daniw/scrutester/hw/ST1-1/Admin/STM32G474 pinout.xlsx

Sheet: Functions
Function | Pin type | Pin quantity | Necessary | Assigned | Remarks
BMS
BMS communication | I2C | 2 | 1 |  | Also connects to EEPROM
BMS wakeup | GPIO | 1 | 1
I_BAT | ADC | 1 | 1
On / off controller
On request | GPIO | 1 | 1
V_IN | ADC | 1 | 1
Converter
Buck-Boost PWM | HRTIM | 4 | 1 | 1 | One channel per bridge
Converter Temperature | ADC | 3 | 1 |  | Number of channels might change
Enable | GPIO | 1 | ? |  | Converter enable still necessary?
Discharge | GPIO | 1 | 1
High voltage converter
Flyback PWM | HRTIM | 1 | 1 | 1
Enable | GPIO | 1 | ? |  | Flyback enable still necessary?
V_HV | ADC | 1 | 1
Overvoltage protection
OVP latch | GPIO | 1 | 1
OVP reset | GPIO | 1 | 1
Current controller
I_1A_REF | DAC | 1 | 1
Shunt enable | GPIO | 1 | 1
Shunt iso enable | GPIO | 1 | 1
Controller temperature | ADC | 1 | 1
Output terminal
V_OUT | ADC | 1 | 1 |  | This measurement does not cover the full output voltage range
OUT_SEL_HV | GPIO | 1 | 1
OUT_SEL_ISO | GPIO | 1 | 1
Measurement
ADC interface | SPI | 4 | 1 | 1
ADC control | GPIO | 3 | 1
V_TERM | ADC | 1 | 1
I_OUT | ADC | 1 | 1
I_ISO | ADC | 1 | 1
User interface
Display | SPI | 4 | 1 | 1
Interface | I2C | 0 | 1 | 0 | Interface shared with BMS
Serial interface | USART | 2 | 1
Encoder | TIM | 2 | 1 | 0.5 | TIM3 or 4
Button | GPIO | 3 | 1
UI present | GPIO | 1 | 1
Infrared interface | IrDA | 2 | 0 |  | USART1, 2, 3, 4, or 5
Microcontroller
Flash | QSPI | 6 | 1 | 1
Programming interface | SWD / JTAG | 4 | 1 | 1
EEPROM | I2C | 0 | 1 | 0 | Interface shared with BMS
Reset | Reset | 1 | 1

Sheet: Timer
Timer overview
Timer Type | Timer | Length | Counter type | Prescaler | Capture / compare channels | Complementary outputs | Encoder
High resolution timer | HRTIM | 16 | Up | 1, 2, 4, (x2, x4, x8, x16, x32 with DLL) | 12 | Yes | No
Advanced motor control | TIM1, TIM8, TIM20 | 16 | Up, down, Up/down | Integer between 1 and 65536 | 4 | 4 | No
General-purpose | TIM2, TIM5 | 32 | Up, down, Up/down | Integer between 1 and 65536 | 4 | No | Yes
General-purpose | TIM3, TIM4 | 16 | Up, down, Up/down | Integer between 1 and 65536 | 4 | No | Yes
General-purpose | TIM15 | 16 | Up | Integer between 1 and 65536 | 2 | 1 | No
General-purpose | TIM16, TIM17 | 16 | Up | Integer between 1 and 65536 | 1 | 2 | No
Basic | TIM6, TIM7 | 16 | Up | Integer between 1 and 65536 | 0 | No | No

Sheet: UART
UART Module | Available RX | Available TX
USART1 | PC5, PE1, (PB7) | PC4, PE0, (PB6)
USART2 | PD6, (PB4) | PD5
UART3 | PB8 | PB9
UART4 | Blocked by SPI | Blocked by SPI
UART5 | PD2 | Blocked by SPI

Sheet: ADC index B
ADC
 |  |  | Signal usage
Signal | Description | Speed | Voltage mode | Current mode | Isolation test | 4W resistance | Voltmeter | Ampmeter | Charging | ADC
V_IN | Input voltage | Fast | Feedforward | Feedforward |  | Feedforward |  |  | Control | 3
V_HV | High-voltage DC-link voltage | Fast |  |  | Control |  |  |  |  | 4
V_TERM | Voltage on output terminals (unfused) | Fast | Control | Control | Control | Feedforward | Validate? |  | Feedforward | 2
I_OUT | Output current (high range) | Fast | Control | Control |  | Control |  | Validate? |  | 1
I_ISO | Isolation measurement current | Fast |  |  | Control |  |  |  |  | 5 | Change to | 3
V_OUT | Output voltage (before fuse) | Fast | Protection |  |  | Control |  |  |  | 4
BMS.I_BAT | Battery current | Fast |  |  |  |  |  |  | Control | 5 | Change to | 2
TEMP_CURRENT | Current controller temperature | Slow |  |  |  | Protection |  |  |  | 3, 4, 5
CONV_CTRL.TEMP_PRIM | Primary MOSFET temperature | Slow | Protection | Protection | Protection | Protection |  |  | Protection | 3, 4, 5
CONV_CTRL.TEMP_SEC | Secondary MOSFET temperature | Slow | Protection | Protection | Protection | Protection |  |  | Protection | 3, 4, 5
CONV_CTRL.TEMP_TRAFO | Transformer temperature | Slow | Protection | Protection | Protection | Protection |  |  | Protection | 3, 4, 5
V_TS | Internal temperature | Slow |  |  |  |  |  |  |  | 1, 5
V_Refint | Reference voltage | Slow | Supervision | Supervision | Supervision | Supervision | Supervision | Supervision | Supervision | 1, 3, 4, 5
V_3V3 | Supply voltage 3.3V | Slow | Supervision | Supervision | Supervision | Supervision | Supervision | Supervision | Supervision | 3, 4, 5
V_3V3_A | Analog supply voltage 3.3V | Slow | Supervision | Supervision | Supervision | Supervision | Supervision | Supervision | Supervision | 3, 4, 5
V_5V | Supply voltage 5V | Slow | Supervision | Supervision | Supervision | Supervision | Supervision | Supervision | Supervision | 3, 4, 5
V_15V | Supply voltage 15V | Slow | Supervision | Supervision | Supervision | Supervision | Supervision | Supervision | Supervision | 3, 4, 5
V_VCC | Supply voltage VCC | Slow | Supervision | Supervision | Supervision | Supervision | Supervision | Supervision | Supervision | 3, 4, 5
 |  |  | ADC usage
Signal | Description | Speed | Voltage mode | Current mode | Isolation test | 4W resistance | Voltmeter | Ampmeter | Charging | ADC | Channel
V_IN | Input voltage | Fast | 3 | 3 |  | 3 |  |  | 3 | 3 | 3
V_HV | High-voltage DC-link voltage | Fast |  |  | 4 |  |  |  |  | 4 | 5 | Pin changed during layouting
V_TERM | Voltage on output terminals (unfused) | Fast | 2 | 2 | 2 | 2 | 2 |  | 2 | 2 | 2 | shared with ADC1
I_OUT | Output current (high range) | Fast | 1 | 1 |  | 1 |  | 1 |  | 1 | 1 | shared with ADC2
I_ISO | Isolation measurement current | Fast |  |  | 5 |  |  |  |  | 5 | 2 | Change to ADC2 channel 2/4
V_OUT | Output voltage (before fuse) | Fast | 4 |  |  | 4 |  |  |  | 4 | 2
BMS.I_BAT | Battery current | Fast |  |  |  |  |  |  | 5 | 5 | 1 | Change to ADC2 channel 5
TEMP_CURRENT | Current controller temperature | Slow |  |  |  | 5 |  |  |  | 3, 4, 5 | 6..12, 14..16
CONV_CTRL.TEMP_PRIM | Primary MOSFET temperature | Slow | 5 | 4, 5 | 3 | 5 |  |  | 4 | 3, 4, 5 | 6..12, 14..16
CONV_CTRL.TEMP_SEC | Secondary MOSFET temperature | Slow | 5 | 4, 5 | 3 | 5 |  |  | 4 | 3, 4, 5 | 6..12, 14..16
CONV_CTRL.TEMP_TRAFO | Transformer temperature | Slow | 5 | 4, 5 | 3 | 5 |  |  | 4 | 3, 4, 5 | 6..12, 14..16
V_TS | Internal temperature | Slow | 5 | 5 | 1 | 5 |  |  | 1 | 1, 5 | 16 (ADC1), 4 (ADC5)
V_Refint | Reference Voltage | Slow | 5 | 5 | 1 | 5 |  |  | 1 | 1, 5 | 18
V_3V3 | Supply voltage 3.3V | Slow | 5 | 4, 5 | 3 | 5 |  |  | 4 | 3, 4, 5 | 6..12, 14..16
V_3V3_A | Analog supply voltage 3.3V | Slow | 5 | 4, 5 | 3 | 5 |  |  | 4 | 3, 4, 5 | 6..12, 14..16
V_5V | Supply voltage 5V | Slow | 5 | 4, 5 | 3 | 5 |  |  | 4 | 3, 4, 5 | 6..12, 14..16
V_15V | Supply voltage 15V | Slow | 5 | 4, 5 | 3 | 5 |  |  | 4 | 3, 4, 5 | 6..12, 14..16
V_VCC | Supply voltage VCC | Slow | 5 | 4, 5 | 3 | 5 |  |  | 4 | 3, 4, 5 | 6..12, 14..16

Sheet: ADC Index C
ADC
 |  |  | Signal usage
Signal | Description | Speed | Voltage mode | Current mode | Isolation test | 4W resistance | Voltmeter | Ampmeter | Charging | ADC
V_IN | Input voltage | Fast | Feedforward | Feedforward |  | Feedforward |  |  | Control | 3
V_HV | High-voltage DC-link voltage | Fast |  |  | Control |  |  |  |  | 4
V_TERM | Voltage on output terminals (unfused) | Fast | Control | Control | Control | Feedforward | Validate? |  | Feedforward | 2
I_OUT | Output current (high range) | Fast | Control | Control |  | Control |  | Validate? |  | 1
I_ISO | Isolation measurement current | Fast |  |  | Control |  |  |  |  | 3
V_OUT | Output voltage (before fuse) | Fast | Protection |  |  | Control |  |  |  | 4
BMS.I_BAT | Battery current | Fast |  |  |  |  |  |  | Control | 2
TEMP_CURRENT | Current controller temperature | Slow |  |  |  | Protection |  |  |  | 3, 4, 5
CONV_CTRL.TEMP_PRIM | Primary MOSFET temperature | Slow | Protection | Protection | Protection | Protection |  |  | Protection | 3, 4, 5
CONV_CTRL.TEMP_SEC | Secondary MOSFET temperature | Slow | Protection | Protection | Protection | Protection |  |  | Protection | 3, 4, 5
CONV_CTRL.TEMP_TRAFO | Transformer temperature | Slow | Protection | Protection | Protection | Protection |  |  | Protection | 3, 4, 5
V_TS | Internal temperature | Slow |  |  |  |  |  |  |  | 1, 5
V_Refint | Reference voltage | Slow | Supervision | Supervision | Supervision | Supervision | Supervision | Supervision | Supervision | 1, 3, 4, 5
V_3V3 | Supply voltage 3.3V | Slow | Supervision | Supervision | Supervision | Supervision | Supervision | Supervision | Supervision | 3, 4, 5
V_3V3_A | Analog supply voltage 3.3V | Slow | Supervision | Supervision | Supervision | Supervision | Supervision | Supervision | Supervision | 3, 4, 5
V_5V | Supply voltage 5V | Slow | Supervision | Supervision | Supervision | Supervision | Supervision | Supervision | Supervision | 3, 4, 5
V_15V | Supply voltage 15V | Slow | Supervision | Supervision | Supervision | Supervision | Supervision | Supervision | Supervision | 3, 4, 5
V_VCC | Supply voltage VCC | Slow | Supervision | Supervision | Supervision | Supervision | Supervision | Supervision | Supervision | 3, 4, 5
 |  |  | ADC usage
Signal | Description | Speed | Voltage mode | Current mode | Isolation test | 4W resistance | Voltmeter | Ampmeter | Charging | ADC | Channel
V_IN | Input voltage | Fast | 3 | 3 |  | 3 |  |  | 3 | 3 | 3
V_HV | High-voltage DC-link voltage | Fast |  |  | 4 |  |  |  |  | 4 | 5 | Pin changed during layouting
V_TERM | Voltage on output terminals (unfused) | Fast | 2 | 2 | 2 | 2 | 2 |  | 2 | 2 | 2 | shared with ADC1
I_OUT | Output current (high range) | Fast | 1 | 1 |  | 1 |  | 1 |  | 1 | 1 | shared with ADC2
I_ISO | Isolation measurement current | Fast |  |  | 2 |  |  |  |  | 2 | 2/4
V_OUT | Output voltage (before fuse) | Fast | 4 |  |  | 4 |  |  |  | 4 | 2
BMS.I_BAT | Battery current | Fast |  |  |  |  |  |  | 2 | 2 | 5
TEMP_CURRENT | Current controller temperature | Slow |  |  |  | 5 |  |  |  | 3, 4, 5 | 6..12, 14..16
CONV_CTRL.TEMP_PRIM | Primary MOSFET temperature | Slow | 5 | 4, 5 | 3 | 5 |  |  | 4 | 3, 4, 5 | 6..12, 14..16
CONV_CTRL.TEMP_SEC | Secondary MOSFET temperature | Slow | 5 | 4, 5 | 3 | 5 |  |  | 4 | 3, 4, 5 | 6..12, 14..16
CONV_CTRL.TEMP_TRAFO | Transformer temperature | Slow | 5 | 4, 5 | 3 | 5 |  |  | 4 | 3, 4, 5 | 6..12, 14..16
V_TS | Internal temperature | Slow | 5 | 5 | 1 | 5 |  |  | 1 | 1, 5 | 16 (ADC1), 4 (ADC5)
V_Refint | Reference Voltage | Slow | 5 | 5 | 1 | 5 |  |  | 1 | 1, 5 | 18
V_3V3 | Supply voltage 3.3V | Slow | 5 | 4, 5 | 3 | 5 |  |  | 4 | 3, 4, 5 | 6..12, 14..16
V_3V3_A | Analog supply voltage 3.3V | Slow | 5 | 4, 5 | 3 | 5 |  |  | 4 | 3, 4, 5 | 6..12, 14..16
V_5V | Supply voltage 5V | Slow | 5 | 4, 5 | 3 | 5 |  |  | 4 | 3, 4, 5 | 6..12, 14..16
V_15V | Supply voltage 15V | Slow | 5 | 4, 5 | 3 | 5 |  |  | 4 | 3, 4, 5 | 6..12, 14..16
V_VCC | Supply voltage VCC | Slow | 5 | 4, 5 | 3 | 5 |  |  | 4 | 3, 4, 5 | 6..12, 14..16

Sheet: Restricted GPIOs
GPIO | Affected Revision | Relevant for application | Errata reference | Restriction
PC13 | All | Yes | 2.2.9 | No toggling when LSE is used on QFP packages
PB10 | All | Yes | 2.8.1 | No toggling while using VREFBUF
PB11 | All except X | Yes | 2.8.1 | No toggling while using VREFBUF
PB13 | All | Yes | 2.8.1 | No toggling while using VREFBUF
PB14 | All except X | Yes | 2.8.1 | No toggling while using VREFBUF
PD14 | All except X | Yes | 2.8.1 | No toggling while using VREFBUF
PA3 | All | No | 2.10.1 | No fast-edge toggle when using OPAMP in non-inverting PGA mode
PA5 | All | No | 2.10.1 | No fast-edge toggle when using OPAMP in non-inverting PGA mode
PB2 | All | No | 2.10.1 | No fast-edge toggle when using OPAMP in non-inverting PGA mode
PB10 | All | No | 2.10.1 | No fast-edge toggle when using OPAMP in non-inverting PGA mode
PB15 | All | No | 2.10.1 | No fast-edge toggle when using OPAMP in non-inverting PGA mode
PA1 | All | No | 2.10.1 | No fast-edge toggle when using OPAMP in non-inverting PGA mode

Sheet: GPIOs QFP100
Pin | GPIO | Restriction | Function
1 | PE2
2 | PE3
3 | PE4
4 | PE5
5 | PE6
6 | VBAT
7 | PC13 | No toggling (LSE)
8 | PC14-OSC32_IN
9 | PC15-OSC32_OUT
10 | PF9
11 | PF10
12 | PF0-OSC_IN
13 | PF1-OSC_OUT
14 | PG10-NRST
15 | PC0
16 | PC1
17 | PC2
18 | PC3
19 | PF2
20 | PA0
21 | PA1
22 | PA2
23 | VSS
24 | VDD
25 | PA3
26 | PA4
27 | PA5
28 | PA6
29 | PA7
30 | PC4
31 | PC5
32 | PB0
33 | PB1
34 | PB2
35 | VSSA
36 | VREF+
37 | VDDA
38 | PE7
39 | PE8
40 | PE9
41 | PE10
42 | PE11
43 | PE12
44 | PE13
45 | PE14
46 | PE15
47 | PB10 | No toggling (VREFBUF)
48 | VSS
49 | VDD
50 | PB11 | No toggling (VREFBUF)
51 | PB12
52 | PB13 | No toggling (VREFBUF)
53 | PB14 | No toggling (VREFBUF)
54 | PB15
55 | PD8
56 | PD9
57 | PD10
58 | PD11
59 | PD12
60 | PD13
61 | PD14 | No toggling (VREFBUF)
62 | PD15
63 | VSS
64 | VDD
65 | PC6
66 | PC7
67 | PC8
68 | PC9
69 | PA8
70 | PA9
71 | PA10
72 | PA11
73 | PA12
74 | VSS
75 | VDD
76 | PA13
77 | PA14
78 | PA15
79 | PC10
80 | PC11
81 | PC12
82 | PD0
83 | PD1
84 | PD2
85 | PD3
86 | PD4
87 | PD5
88 | PD6
89 | PD7
90 | PB3
91 | PB4
92 | PB5
93 | PB6
94 | PB7
95 | PB8-BOOT0
96 | PB89
97 | PE0
98 | PE1
99 | VSS
100 | VDD
