daniw/scrutester/hw/sim/Crowbar_latch.asc

C1: cap; 100n
D1: diode; BAV199HY
D2: diode; BAV199HY
D3: diode; BAV199HY
D4: diode; BAV199HY
D5: diode; 1N5817
I1: current; PULSE(0 20 35m 10m 10m 10m 100m 4)
M1: pmos; BSS84
M2: nmos; BSS123
R1: res; 5m
R2: res; 1k
R3: res; 1k
R4: res; 200k
R5: res; 200k
R6: res; 100k
R7: res; 5.1k
R8: res; 10k
R9: res; 2k
R10: res; 10k
R11: res; 100k
R12: res; 10k
R13: res; 2.4k
R14: res; 100k
U1: TLV314
U2: TLV314
V1: voltage; PULSE(0 3.3 1m 1u 1u 100 200)
V2: voltage; PULSE(0 3.3 150m 1m 1m 10m 50m 2)
Named nets: 0, I_SHUNT, I_OUT, CROWBAR_LATCH, CROWBAR_REF, RESET
.tran 400m
