daniw/scrutester/sw/bat_source/Core/Inc/statemachine.h

/*
 * statemachine.h
 *
 *  Created on: Aug 9, 2025
 *      Author: ahorat
 */

#ifndef INC_STATEMACHINE_H_
#define INC_STATEMACHINE_H_

#include "stdint.h"

#define STATEMACHINE_STEP_PERIOD_mS 20 //ms

typedef enum
{
	  STATEMACHINE_IDLE = 0,
	  STATEMACHINE_MODE_60V_OUT,
	  STATEMACHINE_MODE_10A_OUT,
	  STATEMACHINE_MODE_RESISTANCE_1A,
	  STATEMACHINE_MODE_RESISTANCE_1mA,
	  STATEMACHINE_MODE_ISOMETER,
	  STATEMACHINE_MODE_VOLTMETER,
	  STATEMACHINE_MODE_SETTINGS,
	  STATEMACHINE_MODE_SHUTDOWN,
	  STATEMACHINE_MODE_CHARGE,
	  STATEMACHINE_MODE_AMPMETER,
	  STATEMACHINE_MODE_RESERVED
} statemachine_modes_t;

typedef enum
{
	  STATEMACHINE_SETTINGS_MODE_MENU = 0,
	  STATEMACHINE_SETTINGS_MODE_BMS,
	  STATEMACHINE_SETTINGS_MODE_DISPLAY,
	  STATEMACHINE_SETTINGS_MODE_CALIBRATION,
	  STATEMACHINE_SETTINGS_MODE_ADC1,
	  STATEMACHINE_SETTINGS_MODE_ADC2,
	  STATEMACHINE_SETTINGS_MODE_ABOUT,
	  STATEMACHINE_SETTINGS_MODE_LENGTH
} statemachine_settings_modes_t;

typedef struct{
	statemachine_modes_t current_mode;
	uint8_t output_on;
	uint8_t current_menu_index;
	statemachine_settings_modes_t settings_mode;
	uint8_t protection_forced_output_off;

}statemachine_t;


void statemachine_init(void);
void statemachine_step(void);

void statemachine_switchfromIdle(statemachine_modes_t mode);

#endif /* INC_STATEMACHINE_H_ */
