daniw/scrutester/sw/bat_source/Core/Src/tim.c

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
/* Includes ------------------------------------------------------------------*/
#include "tim.h"

/* USER CODE BEGIN 0 */
#include "irq_priority.h"
/* USER CODE END 0 */

TIM_HandleTypeDef htim2;
TIM_HandleTypeDef htim4;
TIM_HandleTypeDef htim6;
TIM_HandleTypeDef htim16;

/* TIM2 init function */
void MX_TIM2_Init(void)
{

  TIM_ClockConfigTypeDef sClockSourceConfig = {0};
  TIM_MasterConfigTypeDef sMasterConfig = {0};

  htim2.Instance = TIM2;
  htim2.Init.Prescaler = 15999;
  htim2.Init.CounterMode = TIM_COUNTERMODE_UP;
  htim2.Init.Period = 199;
  htim2.Init.ClockDivision = TIM_CLOCKDIVISION_DIV1;
  htim2.Init.AutoReloadPreload = TIM_AUTORELOAD_PRELOAD_ENABLE;
  if (HAL_TIM_Base_Init(&htim2) != HAL_OK)
  {
    Error_Handler();
  }
  sClockSourceConfig.ClockSource = TIM_CLOCKSOURCE_INTERNAL;
  if (HAL_TIM_ConfigClockSource(&htim2, &sClockSourceConfig) != HAL_OK)
  {
    Error_Handler();
  }
  sMasterConfig.MasterOutputTrigger = TIM_TRGO_RESET;
  sMasterConfig.MasterSlaveMode = TIM_MASTERSLAVEMODE_DISABLE;
  if (HAL_TIMEx_MasterConfigSynchronization(&htim2, &sMasterConfig) != HAL_OK)
  {
    Error_Handler();
  }
}
/* TIM4 init function */
void MX_TIM4_Init(void)
{

  /* USER CODE BEGIN TIM4_Init 0 */
  // Timer for Encoder Read
  /* USER CODE END TIM4_Init 0 */

  TIM_Encoder_InitTypeDef sConfig = {0};
  TIM_MasterConfigTypeDef sMasterConfig = {0};

  htim4.Instance = TIM4;
  htim4.Init.Prescaler = 0;
  htim4.Init.CounterMode = TIM_COUNTERMODE_UP;
  htim4.Init.Period = 127;
  htim4.Init.ClockDivision = TIM_CLOCKDIVISION_DIV1;
  htim4.Init.AutoReloadPreload = TIM_AUTORELOAD_PRELOAD_DISABLE;
  sConfig.EncoderMode = TIM_ENCODERMODE_TI1;
  sConfig.IC1Polarity = TIM_ICPOLARITY_FALLING;
  sConfig.IC1Selection = TIM_ICSELECTION_DIRECTTI;
  sConfig.IC1Prescaler = TIM_ICPSC_DIV1;
  sConfig.IC1Filter = 15;
  sConfig.IC2Polarity = TIM_ICPOLARITY_RISING;
  sConfig.IC2Selection = TIM_ICSELECTION_DIRECTTI;
  sConfig.IC2Prescaler = TIM_ICPSC_DIV1;
  sConfig.IC2Filter = 15;
  if (HAL_TIM_Encoder_Init(&htim4, &sConfig) != HAL_OK)
  {
    Error_Handler();
  }
  sMasterConfig.MasterOutputTrigger = TIM_TRGO_RESET;
  sMasterConfig.MasterSlaveMode = TIM_MASTERSLAVEMODE_DISABLE;
  if (HAL_TIMEx_MasterConfigSynchronization(&htim4, &sMasterConfig) != HAL_OK)
  {
    Error_Handler();
  }
  /* USER CODE BEGIN TIM4_Init 2 */

	HAL_TIM_Encoder_Start(&htim4, TIM_CHANNEL_ALL);
  /* USER CODE END TIM4_Init 2 */

}
/* TIM6 init function */
void MX_TIM6_Init(void)
{

  TIM_MasterConfigTypeDef sMasterConfig = {0};

  htim6.Instance = TIM6;
  htim6.Init.Prescaler = 15999;
  htim6.Init.CounterMode = TIM_COUNTERMODE_UP;
  htim6.Init.Period = 4999;
  htim6.Init.AutoReloadPreload = TIM_AUTORELOAD_PRELOAD_ENABLE;
  if (HAL_TIM_Base_Init(&htim6) != HAL_OK)
  {
    Error_Handler();
  }
  sMasterConfig.MasterOutputTrigger = TIM_TRGO_RESET;
  sMasterConfig.MasterSlaveMode = TIM_MASTERSLAVEMODE_DISABLE;
  if (HAL_TIMEx_MasterConfigSynchronization(&htim6, &sMasterConfig) != HAL_OK)
  {
    Error_Handler();
  }
  /* USER CODE BEGIN TIM6_Init 2 */
  HAL_TIM_Base_Start_IT(&htim6);
  /* USER CODE END TIM6_Init 2 */

}
/* TIM16 init function */
void MX_TIM16_Init(void)
{

  /* USER CODE BEGIN TIM16_Init 0 */
	// Timer for ext ADC Clock
  /* USER CODE END TIM16_Init 0 */

  TIM_OC_InitTypeDef sConfigOC = {0};
  TIM_BreakDeadTimeConfigTypeDef sBreakDeadTimeConfig = {0};

  htim16.Instance = TIM16;
  htim16.Init.Prescaler = 0;
  htim16.Init.CounterMode = TIM_COUNTERMODE_UP;
  htim16.Init.Period = 19;
  htim16.Init.ClockDivision = TIM_CLOCKDIVISION_DIV1;
  htim16.Init.RepetitionCounter = 0;
  htim16.Init.AutoReloadPreload = TIM_AUTORELOAD_PRELOAD_DISABLE;
  if (HAL_TIM_Base_Init(&htim16) != HAL_OK)
  {
    Error_Handler();
  }
  if (HAL_TIM_PWM_Init(&htim16) != HAL_OK)
  {
    Error_Handler();
  }
  sConfigOC.OCMode = TIM_OCMODE_PWM1;
  sConfigOC.Pulse = 10;
  sConfigOC.OCPolarity = TIM_OCPOLARITY_HIGH;
  sConfigOC.OCNPolarity = TIM_OCNPOLARITY_HIGH;
  sConfigOC.OCFastMode = TIM_OCFAST_ENABLE;
  sConfigOC.OCIdleState = TIM_OCIDLESTATE_RESET;
  sConfigOC.OCNIdleState = TIM_OCNIDLESTATE_RESET;
  if (HAL_TIM_PWM_ConfigChannel(&htim16, &sConfigOC, TIM_CHANNEL_1) != HAL_OK)
  {
    Error_Handler();
  }
  sBreakDeadTimeConfig.OffStateRunMode = TIM_OSSR_DISABLE;
  sBreakDeadTimeConfig.OffStateIDLEMode = TIM_OSSI_DISABLE;
  sBreakDeadTimeConfig.LockLevel = TIM_LOCKLEVEL_OFF;
  sBreakDeadTimeConfig.DeadTime = 0;
  sBreakDeadTimeConfig.BreakState = TIM_BREAK_DISABLE;
  sBreakDeadTimeConfig.BreakPolarity = TIM_BREAKPOLARITY_HIGH;
  sBreakDeadTimeConfig.BreakFilter = 0;
  sBreakDeadTimeConfig.AutomaticOutput = TIM_AUTOMATICOUTPUT_ENABLE;
  if (HAL_TIMEx_ConfigBreakDeadTime(&htim16, &sBreakDeadTimeConfig) != HAL_OK)
  {
    Error_Handler();
  }
  /* USER CODE BEGIN TIM16_Init 2 */
  HAL_TIM_Base_Start(&htim16);
  HAL_TIM_PWM_Start(&htim16, TIM_CHANNEL_1);
  /* USER CODE END TIM16_Init 2 */
  HAL_TIM_MspPostInit(&htim16);

}

void HAL_TIM_Base_MspInit(TIM_HandleTypeDef* tim_baseHandle)
{

  if(tim_baseHandle->Instance==TIM2)
  {
    /* TIM2 clock enable */
    __HAL_RCC_TIM2_CLK_ENABLE();

    /* TIM2 interrupt Init -- state machine tick, millisecond-scale. */
    HAL_NVIC_SetPriority(TIM2_IRQn, IRQ_PRIO_AUX, IRQ_SUBPRIO_NONE);
    HAL_NVIC_EnableIRQ(TIM2_IRQn);
  }
  else if(tim_baseHandle->Instance==TIM6)
  {
    /* TIM6 clock enable */
    __HAL_RCC_TIM6_CLK_ENABLE();

    /* TIM6 interrupt Init -- DAC square wave for the 1A resistance test.
     * NOTE: TIM6_DAC_IRQn's priority is also set in dac.c's MX_DAC1_Init()
     * (duplicate registration, whichever HAL init runs last wins at
     * runtime) -- both call sites now use IRQ_PRIO_AUX so the outcome no
     * longer depends on init order. */
    HAL_NVIC_SetPriority(TIM6_DAC_IRQn, IRQ_PRIO_AUX, IRQ_SUBPRIO_NONE);
    HAL_NVIC_EnableIRQ(TIM6_DAC_IRQn);
  }
  else if(tim_baseHandle->Instance==TIM16)
  {
    /* TIM16 clock enable */
    __HAL_RCC_TIM16_CLK_ENABLE();
  }
}

void HAL_TIM_Encoder_MspInit(TIM_HandleTypeDef* tim_encoderHandle)
{

  GPIO_InitTypeDef GPIO_InitStruct = {0};
  if(tim_encoderHandle->Instance==TIM4)
  {
    /* TIM4 clock enable */
    __HAL_RCC_TIM4_CLK_ENABLE();

    __HAL_RCC_GPIOB_CLK_ENABLE();
    /**TIM4 GPIO Configuration
    PB6     ------> TIM4_CH1
    PB7     ------> TIM4_CH2
    */
    GPIO_InitStruct.Pin = ENCODER_B_Pin|ENCODER_A_Pin;
    GPIO_InitStruct.Mode = GPIO_MODE_AF_PP;
    GPIO_InitStruct.Pull = GPIO_NOPULL;
    GPIO_InitStruct.Speed = GPIO_SPEED_FREQ_LOW;
    GPIO_InitStruct.Alternate = GPIO_AF2_TIM4;
    HAL_GPIO_Init(GPIOB, &GPIO_InitStruct);

  }
}
void HAL_TIM_MspPostInit(TIM_HandleTypeDef* timHandle)
{

  GPIO_InitTypeDef GPIO_InitStruct = {0};
  if(timHandle->Instance==TIM16)
  {
    __HAL_RCC_GPIOA_CLK_ENABLE();
    /**TIM16 GPIO Configuration
    PA12     ------> TIM16_CH1
    */
    GPIO_InitStruct.Pin = ADC_CLK_Pin;
    GPIO_InitStruct.Mode = GPIO_MODE_AF_PP;
    GPIO_InitStruct.Pull = GPIO_NOPULL;
    GPIO_InitStruct.Speed = GPIO_SPEED_FREQ_VERY_HIGH;
    GPIO_InitStruct.Alternate = GPIO_AF1_TIM16;
    HAL_GPIO_Init(ADC_CLK_GPIO_Port, &GPIO_InitStruct);

  }

}

void HAL_TIM_Base_MspDeInit(TIM_HandleTypeDef* tim_baseHandle)
{

  if(tim_baseHandle->Instance==TIM2)
  {
    /* Peripheral clock disable */
    __HAL_RCC_TIM2_CLK_DISABLE();

    /* TIM2 interrupt Deinit */
    HAL_NVIC_DisableIRQ(TIM2_IRQn);
  }
  else if(tim_baseHandle->Instance==TIM6)
  {
    /* Peripheral clock disable */
    __HAL_RCC_TIM6_CLK_DISABLE();

    /* TIM6 interrupt Deinit */
  /* USER CODE BEGIN TIM6:TIM6_DAC_IRQn disable */
    /**
    * Uncomment the line below to disable the "TIM6_DAC_IRQn" interrupt
    * Be aware, disabling shared interrupt may affect other IPs
    */
    /* HAL_NVIC_DisableIRQ(TIM6_DAC_IRQn); */
  /* USER CODE END TIM6:TIM6_DAC_IRQn disable */

  }
  else if(tim_baseHandle->Instance==TIM16)
  {
    /* Peripheral clock disable */
    __HAL_RCC_TIM16_CLK_DISABLE();
  }
}

void HAL_TIM_Encoder_MspDeInit(TIM_HandleTypeDef* tim_encoderHandle)
{

  if(tim_encoderHandle->Instance==TIM4)
  {
    /* Peripheral clock disable */
    __HAL_RCC_TIM4_CLK_DISABLE();

    /**TIM4 GPIO Configuration
    PB6     ------> TIM4_CH1
    PB7     ------> TIM4_CH2
    */
    HAL_GPIO_DeInit(GPIOB, ENCODER_B_Pin|ENCODER_A_Pin);

  }
}
