daniw/scrutester/sw/bat_source/Core/Src/spi.c

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
/* Includes ------------------------------------------------------------------*/
#include "spi.h"

/* USER CODE BEGIN 0 */
#include "irq_priority.h"
/* USER CODE END 0 */

SPI_HandleTypeDef hspi3;
SPI_HandleTypeDef hspi4;
DMA_HandleTypeDef hdma_spi3_rx;
DMA_HandleTypeDef hdma_spi3_tx;
DMA_HandleTypeDef hdma_spi4_tx;

/* SPI3 init function */
void MX_SPI3_Init(void)
{

  hspi3.Instance = SPI3;
  hspi3.Init.Mode = SPI_MODE_MASTER;
  hspi3.Init.Direction = SPI_DIRECTION_2LINES;
  hspi3.Init.DataSize = SPI_DATASIZE_8BIT;
  hspi3.Init.CLKPolarity = SPI_POLARITY_LOW;
  hspi3.Init.CLKPhase = SPI_PHASE_2EDGE;
  hspi3.Init.NSS = SPI_NSS_SOFT;
  hspi3.Init.BaudRatePrescaler = SPI_BAUDRATEPRESCALER_8;
  hspi3.Init.FirstBit = SPI_FIRSTBIT_MSB;
  hspi3.Init.TIMode = SPI_TIMODE_DISABLE;
  hspi3.Init.CRCCalculation = SPI_CRCCALCULATION_DISABLE;
  hspi3.Init.CRCPolynomial = 7;
  hspi3.Init.CRCLength = SPI_CRC_LENGTH_DATASIZE;
  hspi3.Init.NSSPMode = SPI_NSS_PULSE_DISABLE;
  if (HAL_SPI_Init(&hspi3) != HAL_OK)
  {
    Error_Handler();
  }
}
/* SPI4 init function */
void MX_SPI4_Init(void)
{

  hspi4.Instance = SPI4;
  hspi4.Init.Mode = SPI_MODE_MASTER;
  hspi4.Init.Direction = SPI_DIRECTION_2LINES;
  hspi4.Init.DataSize = SPI_DATASIZE_16BIT;
  hspi4.Init.CLKPolarity = SPI_POLARITY_LOW;
  hspi4.Init.CLKPhase = SPI_PHASE_1EDGE;
  hspi4.Init.NSS = SPI_NSS_SOFT;
  hspi4.Init.BaudRatePrescaler = SPI_BAUDRATEPRESCALER_4;
  hspi4.Init.FirstBit = SPI_FIRSTBIT_MSB;
  hspi4.Init.TIMode = SPI_TIMODE_DISABLE;
  hspi4.Init.CRCCalculation = SPI_CRCCALCULATION_DISABLE;
  hspi4.Init.CRCPolynomial = 7;
  hspi4.Init.CRCLength = SPI_CRC_LENGTH_DATASIZE;
  hspi4.Init.NSSPMode = SPI_NSS_PULSE_DISABLE;
  if (HAL_SPI_Init(&hspi4) != HAL_OK)
  {
    Error_Handler();
  }
}

void HAL_SPI_MspInit(SPI_HandleTypeDef* spiHandle)
{

  GPIO_InitTypeDef GPIO_InitStruct = {0};
  if(spiHandle->Instance==SPI3)
  {
    /* SPI3 clock enable */
    __HAL_RCC_SPI3_CLK_ENABLE();

    __HAL_RCC_GPIOC_CLK_ENABLE();
    /**SPI3 GPIO Configuration
    PC10     ------> SPI3_SCK
    PC11     ------> SPI3_MISO
    PC12     ------> SPI3_MOSI
    */
    GPIO_InitStruct.Pin = SPI_SCK_Pin|SPI_MISO_Pin|SPI_MOSI_Pin;
    GPIO_InitStruct.Mode = GPIO_MODE_AF_PP;
    GPIO_InitStruct.Pull = GPIO_NOPULL;
    GPIO_InitStruct.Speed = GPIO_SPEED_FREQ_VERY_HIGH;
    GPIO_InitStruct.Alternate = GPIO_AF6_SPI3;
    HAL_GPIO_Init(GPIOC, &GPIO_InitStruct);

    /* SPI3 DMA Init */
    /* SPI3_RX Init */
    hdma_spi3_rx.Instance = DMA1_Channel6;
    hdma_spi3_rx.Init.Request = DMA_REQUEST_SPI3_RX;
    hdma_spi3_rx.Init.Direction = DMA_PERIPH_TO_MEMORY;
    hdma_spi3_rx.Init.PeriphInc = DMA_PINC_DISABLE;
    hdma_spi3_rx.Init.MemInc = DMA_MINC_ENABLE;
    hdma_spi3_rx.Init.PeriphDataAlignment = DMA_PDATAALIGN_BYTE;
    hdma_spi3_rx.Init.MemDataAlignment = DMA_MDATAALIGN_BYTE;
    hdma_spi3_rx.Init.Mode = DMA_NORMAL;
    hdma_spi3_rx.Init.Priority = DMA_PRIORITY_LOW;
    if (HAL_DMA_Init(&hdma_spi3_rx) != HAL_OK)
    {
      Error_Handler();
    }

    __HAL_LINKDMA(spiHandle,hdmarx,hdma_spi3_rx);

    /* SPI3_TX Init */
    hdma_spi3_tx.Instance = DMA1_Channel7;
    hdma_spi3_tx.Init.Request = DMA_REQUEST_SPI3_TX;
    hdma_spi3_tx.Init.Direction = DMA_MEMORY_TO_PERIPH;
    hdma_spi3_tx.Init.PeriphInc = DMA_PINC_DISABLE;
    hdma_spi3_tx.Init.MemInc = DMA_MINC_ENABLE;
    hdma_spi3_tx.Init.PeriphDataAlignment = DMA_PDATAALIGN_BYTE;
    hdma_spi3_tx.Init.MemDataAlignment = DMA_MDATAALIGN_BYTE;
    hdma_spi3_tx.Init.Mode = DMA_NORMAL;
    hdma_spi3_tx.Init.Priority = DMA_PRIORITY_LOW;
    if (HAL_DMA_Init(&hdma_spi3_tx) != HAL_OK)
    {
      Error_Handler();
    }

    __HAL_LINKDMA(spiHandle,hdmatx,hdma_spi3_tx);

    /* SPI3 interrupt Init -- ADS131M04 external-ADC pipeline, same tier as
     * its DMA channels and the DRDY EXTI2 line (ads131m04.c). */
    HAL_NVIC_SetPriority(SPI3_IRQn, IRQ_PRIO_EXT_ADC, IRQ_SUBPRIO_NONE);
    HAL_NVIC_EnableIRQ(SPI3_IRQn);
  }
  else if(spiHandle->Instance==SPI4)
  {
    /* SPI4 clock enable */
    __HAL_RCC_SPI4_CLK_ENABLE();

    __HAL_RCC_GPIOE_CLK_ENABLE();
    /**SPI4 GPIO Configuration
    PE2     ------> SPI4_SCK
    PE5     ------> SPI4_MISO
    PE6     ------> SPI4_MOSI
    */
    GPIO_InitStruct.Pin = DISPLAY_SCK_Pin|DISPLAY_MISO_Pin|DISPLAY_MOSI_Pin;
    GPIO_InitStruct.Mode = GPIO_MODE_AF_PP;
    GPIO_InitStruct.Pull = GPIO_NOPULL;
    GPIO_InitStruct.Speed = GPIO_SPEED_FREQ_VERY_HIGH;
    GPIO_InitStruct.Alternate = GPIO_AF5_SPI4;
    HAL_GPIO_Init(GPIOE, &GPIO_InitStruct);

    /* SPI4 DMA Init */
    /* SPI4_TX Init */
    hdma_spi4_tx.Instance = DMA2_Channel2;
    hdma_spi4_tx.Init.Request = DMA_REQUEST_SPI4_TX;
    hdma_spi4_tx.Init.Direction = DMA_MEMORY_TO_PERIPH;
    hdma_spi4_tx.Init.PeriphInc = DMA_PINC_DISABLE;
    hdma_spi4_tx.Init.MemInc = DMA_MINC_ENABLE;
    hdma_spi4_tx.Init.PeriphDataAlignment = DMA_PDATAALIGN_BYTE;
    hdma_spi4_tx.Init.MemDataAlignment = DMA_MDATAALIGN_BYTE;
    hdma_spi4_tx.Init.Mode = DMA_NORMAL;
    hdma_spi4_tx.Init.Priority = DMA_PRIORITY_LOW;
    if (HAL_DMA_Init(&hdma_spi4_tx) != HAL_OK)
    {
      Error_Handler();
    }

    __HAL_LINKDMA(spiHandle,hdmatx,hdma_spi4_tx);

    /* SPI4 interrupt Init -- LCD, non-time-critical. */
    HAL_NVIC_SetPriority(SPI4_IRQn, IRQ_PRIO_AUX, IRQ_SUBPRIO_NONE);
    HAL_NVIC_EnableIRQ(SPI4_IRQn);
  }
}

void HAL_SPI_MspDeInit(SPI_HandleTypeDef* spiHandle)
{

  if(spiHandle->Instance==SPI3)
  {
    /* Peripheral clock disable */
    __HAL_RCC_SPI3_CLK_DISABLE();

    /**SPI3 GPIO Configuration
    PC10     ------> SPI3_SCK
    PC11     ------> SPI3_MISO
    PC12     ------> SPI3_MOSI
    */
    HAL_GPIO_DeInit(GPIOC, SPI_SCK_Pin|SPI_MISO_Pin|SPI_MOSI_Pin);

    /* SPI3 DMA DeInit */
    HAL_DMA_DeInit(spiHandle->hdmarx);
    HAL_DMA_DeInit(spiHandle->hdmatx);

    /* SPI3 interrupt Deinit */
    HAL_NVIC_DisableIRQ(SPI3_IRQn);
  }
  else if(spiHandle->Instance==SPI4)
  {
    /* Peripheral clock disable */
    __HAL_RCC_SPI4_CLK_DISABLE();

    /**SPI4 GPIO Configuration
    PE2     ------> SPI4_SCK
    PE5     ------> SPI4_MISO
    PE6     ------> SPI4_MOSI
    */
    HAL_GPIO_DeInit(GPIOE, DISPLAY_SCK_Pin|DISPLAY_MISO_Pin|DISPLAY_MOSI_Pin);

    /* SPI4 DMA DeInit */
    HAL_DMA_DeInit(spiHandle->hdmatx);

    /* SPI4 interrupt Deinit */
    HAL_NVIC_DisableIRQ(SPI4_IRQn);
  }
}

/* USER CODE BEGIN 1 */

/*
 * @brief Sets SPI interface baud rate
 * @param spiHandle Handle to the spi interface to be configured
 * @param prescaler Prescaler to be used, supported values: 2, 4, 8, 16, 32, 64, 128, 256
 * @return Status
 */

HAL_StatusTypeDef SPI_set_prescaler(SPI_HandleTypeDef* spiHandle, uint16_t prescaler) {
	switch (prescaler) {
	case 2:
		spiHandle->Init.BaudRatePrescaler = SPI_BAUDRATEPRESCALER_2;
		break;
	case 4:
		spiHandle->Init.BaudRatePrescaler = SPI_BAUDRATEPRESCALER_4;
		break;
	case 8:
		spiHandle->Init.BaudRatePrescaler = SPI_BAUDRATEPRESCALER_8;
		break;
	case 16:
		spiHandle->Init.BaudRatePrescaler = SPI_BAUDRATEPRESCALER_16;
		break;
	case 32:
		spiHandle->Init.BaudRatePrescaler = SPI_BAUDRATEPRESCALER_32;
		break;
	case 64:
		spiHandle->Init.BaudRatePrescaler = SPI_BAUDRATEPRESCALER_64;
		break;
	case 128:
		spiHandle->Init.BaudRatePrescaler = SPI_BAUDRATEPRESCALER_128;
		break;
	case 256:
		spiHandle->Init.BaudRatePrescaler = SPI_BAUDRATEPRESCALER_256;
		break;
	default:
		return HAL_ERROR;
	}
    return HAL_SPI_Init(spiHandle);
}
/* USER CODE END 1 */
