daniw/scrutester/sw/bat_source/Core/Inc/version.h

/*
 * version.h
 *
 * Manually-bumped firmware version, shown on the Settings > About page
 * alongside the compiler-generated build date/time (see display.c).
 */

#ifndef INC_VERSION_H_
#define INC_VERSION_H_

#define FW_VERSION_MAJOR 0
#define FW_VERSION_MINOR 1

#endif /* INC_VERSION_H_ */
