daniw/scrutester/sw/bat_source/Core/Inc/hrtim.h

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
/* Define to prevent recursive inclusion -------------------------------------*/
#ifndef __HRTIM_H__
#define __HRTIM_H__

#ifdef __cplusplus
extern "C" {
#endif

/* Includes ------------------------------------------------------------------*/
#include "main.h"

extern HRTIM_HandleTypeDef hhrtim1;

/* USER CODE BEGIN Private defines */
/* HRTIM_CHANNEL_PRIM/SEK/HV are indices into HRTIM1->sTimerxRegs[] (Timer
 * B/E/C respectively). HRTIM_CHANNEL_ALL is a software-only sentinel used by
 * hrtim_disable() to mean "every channel at once" - it must NOT collide with
 * any real sTimerxRegs[] index (0..5, Timers A..F), otherwise a function
 * that doesn't special-case ALL would read/write Timer A's registers. */
#define HRTIM_CHANNEL_ALL 0xFF
#define HRTIM_CHANNEL_PRIM 1
#define HRTIM_CHANNEL_SEK 4
#define HRTIM_CHANNEL_HV 2
/* USER CODE END Private defines */

void MX_HRTIM1_Init(void);

void HAL_HRTIM_MspPostInit(HRTIM_HandleTypeDef *hhrtim);

/* USER CODE BEGIN Prototypes */
void hrtim_start_timer(void);
void hrtim_set_freq(uint8_t channel, uint32_t freq);
void hrtim_set_duty(uint8_t channel, float value);
void hrtim_enable(uint8_t channel);
void hrtim_disable(uint8_t channel);
void hrtim_sek_force_short(void);
void hrtim_sek_restore(void);
/* USER CODE END Prototypes */

#ifdef __cplusplus
}
#endif

#endif /* __HRTIM_H__ */
