daniw/scrutester/sw/bat_source/Core/Src/calibration.c

/*
 * calibration.c
 *
 * See calibration.h.
 */

#include "calibration.h"
#include "adc.h"
#include "config_store.h"
#include "statemachine.h"
#include "stm32g4xx_hal.h"
#include <math.h>

extern ADC_MEAS_DATA adc_data;

#define CALIBRATION_SAMPLE_COUNT 8
#define CALIBRATION_SAMPLE_DELAY_MS 1

/* Bounds for a computed/supplied gain to be accepted by
 * calibration_set_gain()/calibration_set_gain_raw(). The real per-channel
 * gains (adc.h's ADC_*_GAIN_* / ADC_EXT_*_GAIN_* constants) range from
 * about 0.0014 (ADC_EXT_IISO_GAIN_UA) to about 296 (ADC_VTERM_GAIN_MV) --
 * i.e. roughly 0.001..300. CALIBRATION_GAIN_MAX_MAGNITUDE is set to
 * 10000, about 33x the largest real gain: generous enough that no
 * legitimate calibration (sampled or hand-typed) is ever rejected, but
 * still tight enough to catch the actual failure mode -- raw barely
 * moving off the offset (a couple of ADC counts) while a large reference
 * was dialed in/typed, e.g. a disconnected or short-circuited input --
 * which otherwise produces a gain in the thousands-to-millions range.
 * A gain of exactly 0 (or too small to be distinguishable from 0 in
 * practice) is never valid either: it corresponds to raw == offset or a
 * zero reference, both of which mean "no real second calibration point
 * was actually applied". */
#define CALIBRATION_GAIN_MAX_MAGNITUDE 10000.0f
#define CALIBRATION_GAIN_MIN_MAGNITUDE 1e-6f

static uint8_t calibration_gain_valid(float gain) {
	float mag = fabsf(gain);
	return isfinite(gain) && mag >= CALIBRATION_GAIN_MIN_MAGNITUDE
			&& mag <= CALIBRATION_GAIN_MAX_MAGNITUDE;
}

static const char *const CAL_CHANNEL_NAMES[CAL_CH_COUNT] = {
		[CAL_CH_V_TERM] = "V_TERM",
		[CAL_CH_V_SENS] = "V_SENS",
		[CAL_CH_V_OUT] = "V_OUT",
		[CAL_CH_V_HV] = "V_HV",
		[CAL_CH_I_OUT] = "I_OUT",
		[CAL_CH_I_ISO] = "I_ISO",
		[CAL_CH_V_IN] = "V_IN", };

static const char *const CAL_CHANNEL_UNITS[CAL_CH_COUNT] = {
		[CAL_CH_V_TERM] = "mV",
		[CAL_CH_V_SENS] = "uV",
		[CAL_CH_V_OUT] = "mV",
		[CAL_CH_V_HV] = "mV",
		[CAL_CH_I_OUT] = "mA",
		[CAL_CH_I_ISO] = "uA",
		[CAL_CH_V_IN] = "mV", };

const char* calibration_channel_name(calibration_channel_t ch) {
	if (ch >= CAL_CH_COUNT)
		return "?";
	return CAL_CHANNEL_NAMES[ch];
}

const char* calibration_channel_unit(calibration_channel_t ch) {
	if (ch >= CAL_CH_COUNT)
		return "?";
	return CAL_CHANNEL_UNITS[ch];
}

/* V_OUT/V_HV (and I_ISO's injected channel) are only sampled by ADC4/5
 * while adc_configure_mode() has configured them for a specific
 * statemachine mode (see adc.c) - the Settings/Calibration screen
 * itself never does, since it never drives the output. Point the
 * relevant ADC(s) at the right channel before sampling; harmless to
 * call repeatedly (aux IO / output-enable are untouched by this call). */
void calibration_ensure_adc_mode(calibration_channel_t ch) {
	switch (ch) {
	case CAL_CH_V_OUT:
		adc_configure_mode(STATEMACHINE_MODE_60V_OUT);
		break;
	case CAL_CH_V_HV:
	case CAL_CH_I_ISO:
		adc_configure_mode(STATEMACHINE_MODE_ISOMETER);
		break;
	default:
		adc_configure_mode(STATEMACHINE_MODE_SETTINGS);
		break;
	}
}

static int32_t calibration_sample_raw_once(calibration_channel_t ch) {
	switch (ch) {
	case CAL_CH_V_TERM:
		return (int32_t) adc_data.raw.v_term;
	case CAL_CH_V_SENS:
		return adc_data.ext_adc_data[2];
	case CAL_CH_V_OUT:
		return (int32_t) adc_data.raw.v_out;
	case CAL_CH_V_HV:
		return (int32_t) adc_data.raw.v_hv;
	case CAL_CH_I_OUT:
		return (int32_t) adc_data.raw.i_out;
	case CAL_CH_I_ISO:
		return (int32_t) adc_data.raw.i_iso;
	case CAL_CH_V_IN:
		return (int32_t) adc_data.raw.v_in;
	default:
		return 0;
	}
}

int32_t calibration_read_raw(calibration_channel_t ch) {
	int64_t sum = 0;

	calibration_ensure_adc_mode(ch);
	for (uint8_t i = 0; i < CALIBRATION_SAMPLE_COUNT; i++) {
		sum += calibration_sample_raw_once(ch);
		HAL_Delay(CALIBRATION_SAMPLE_DELAY_MS);
	}
	return (int32_t) (sum / CALIBRATION_SAMPLE_COUNT);
}

/* Non-blocking: no averaging, no calibration_ensure_adc_mode() call.
 * Relies on the caller having already armed ch (see calibration.h). */
int32_t calibration_peek_raw(calibration_channel_t ch) {
	return calibration_sample_raw_once(ch);
}

/* V_TERM/I_OUT/I_ISO each have an external-ADC (ADS131M04) counterpart
 * that is not itself a selectable calibration channel: it is sampled
 * continuously and independently by the ext ADC's own DRDY/SPI loop,
 * measuring the same physical quantity at the same time as the
 * internal channel. Returns the ext_adc_data[] index for channels that
 * have such a counterpart, or -1 for those that don't. */
static int32_t calibration_ext_index(calibration_channel_t ch) {
	switch (ch) {
	case CAL_CH_V_TERM:
		return 0;
	case CAL_CH_I_OUT:
		return 1;
	case CAL_CH_I_ISO:
		return 3;
	default:
		return -1;
	}
}

uint8_t calibration_has_ext(calibration_channel_t ch) {
	return calibration_ext_index(ch) >= 0;
}

/* Non-blocking counterpart -- see calibration_peek_raw()'s comment. */
int32_t calibration_peek_ext_converted(calibration_channel_t ch) {
	switch (ch) {
	case CAL_CH_V_TERM:
		return adc_data.converted.v_term_ext_mv;
	case CAL_CH_I_OUT:
		return adc_data.converted.i_out_ext_mA;
	case CAL_CH_I_ISO:
		return adc_data.converted.i_iso_ext_uA;
	default:
		return 0;
	}
}

int32_t calibration_read_ext_converted(calibration_channel_t ch) {
	calibration_ensure_adc_mode(ch);
	return calibration_peek_ext_converted(ch);
}

static int32_t calibration_get_ext_offset(calibration_channel_t ch) {
	switch (ch) {
	case CAL_CH_V_TERM:
		return adc_data.v_term_ext_offset;
	case CAL_CH_I_OUT:
		return adc_data.i_out_ext_offset;
	case CAL_CH_I_ISO:
		return adc_data.i_iso_ext_offset;
	default:
		return 0;
	}
}

/* Samples the internal raw value for ch (same as calibration_read_raw())
 * and, when ch has an ext counterpart, its ext raw value - both in the
 * same CALIBRATION_SAMPLE_COUNT-iteration loop, so both are averaged
 * over the same sampling window. *raw_ext_out is left at 0 when ch has
 * no ext counterpart. */
static void calibration_sample_pair(calibration_channel_t ch, int32_t *raw_out, int32_t *raw_ext_out) {
	int64_t sum = 0;
	int64_t sum_ext = 0;
	int32_t ext_index = calibration_ext_index(ch);

	calibration_ensure_adc_mode(ch);
	for (uint8_t i = 0; i < CALIBRATION_SAMPLE_COUNT; i++) {
		sum += calibration_sample_raw_once(ch);
		if (ext_index >= 0)
			sum_ext += adc_data.ext_adc_data[ext_index];
		HAL_Delay(CALIBRATION_SAMPLE_DELAY_MS);
	}
	*raw_out = (int32_t) (sum / CALIBRATION_SAMPLE_COUNT);
	*raw_ext_out = (int32_t) (sum_ext / CALIBRATION_SAMPLE_COUNT);
}

/* Non-blocking counterpart -- see calibration_peek_raw()'s comment. */
int32_t calibration_peek_converted(calibration_channel_t ch) {
	switch (ch) {
	case CAL_CH_V_TERM:
		return adc_data.converted.v_term;
	case CAL_CH_V_SENS:
		return adc_data.converted.v_sens_ext_uv;
	case CAL_CH_V_OUT:
		return (int32_t) adc_data.converted.v_out;
	case CAL_CH_V_HV:
		return (int32_t) adc_data.converted.v_hv;
	case CAL_CH_I_OUT:
		return adc_data.converted.i_out;
	case CAL_CH_I_ISO:
		return adc_data.converted.i_iso;
	case CAL_CH_V_IN:
		return adc_data.converted.v_in;
	default:
		return 0;
	}
}

int32_t calibration_read_converted(calibration_channel_t ch) {
	calibration_ensure_adc_mode(ch);
	return calibration_peek_converted(ch);
}

static int32_t calibration_get_offset(calibration_channel_t ch) {
	switch (ch) {
	case CAL_CH_V_TERM:
		return adc_data.v_term_offset;
	case CAL_CH_V_SENS:
		return adc_data.v_sens_ext_offset;
	case CAL_CH_V_OUT:
		return adc_data.v_out_offset;
	case CAL_CH_V_HV:
		return adc_data.v_hv_offset;
	case CAL_CH_I_OUT:
		return adc_data.i_out_offset;
	case CAL_CH_I_ISO:
		return adc_data.i_iso_offset;
	case CAL_CH_V_IN:
		return adc_data.v_in_offset;
	default:
		return 0;
	}
}

void calibration_zero(calibration_channel_t ch) {
	int32_t raw, raw_ext;

	calibration_sample_pair(ch, &raw, &raw_ext);

	switch (ch) {
	case CAL_CH_V_TERM:
		adc_data.v_term_offset = (uint16_t) raw;
		config_store.calibration.v_term_offset_mv = (uint16_t) raw;
		adc_data.v_term_ext_offset = raw_ext;
		config_store.calibration.v_term_ext_offset = raw_ext;
		break;
	case CAL_CH_V_SENS:
		adc_data.v_sens_ext_offset = raw;
		config_store.calibration.v_sens_ext_offset = raw;
		break;
	case CAL_CH_V_OUT:
		adc_data.v_out_offset = (uint16_t) raw;
		config_store.calibration.v_out_offset = (uint16_t) raw;
		break;
	case CAL_CH_V_HV:
		adc_data.v_hv_offset = (uint16_t) raw;
		config_store.calibration.v_hv_offset = (uint16_t) raw;
		break;
	case CAL_CH_I_OUT:
		adc_data.i_out_offset = (uint16_t) raw;
		config_store.calibration.i_out_offset_ma = (uint16_t) raw;
		adc_data.i_out_ext_offset = raw_ext;
		config_store.calibration.i_out_ext_offset = raw_ext;
		break;
	case CAL_CH_I_ISO:
		adc_data.i_iso_offset = (uint16_t) raw;
		config_store.calibration.i_iso_offset_ua = (uint16_t) raw;
		adc_data.i_iso_ext_offset = raw_ext;
		config_store.calibration.i_iso_ext_offset = raw_ext;
		break;
	case CAL_CH_V_IN:
		adc_data.v_in_offset = (uint16_t) raw;
		config_store.calibration.v_in_offset_mv = (uint16_t) raw;
		break;
	default:
		return;
	}
	config_store_store();
}

void calibration_set_offset_raw(calibration_channel_t ch, int32_t raw_offset, const int32_t *raw_ext_offset) {
	switch (ch) {
	case CAL_CH_V_TERM:
		adc_data.v_term_offset = (uint16_t) raw_offset;
		config_store.calibration.v_term_offset_mv = (uint16_t) raw_offset;
		if (raw_ext_offset) {
			adc_data.v_term_ext_offset = *raw_ext_offset;
			config_store.calibration.v_term_ext_offset = *raw_ext_offset;
		}
		break;
	case CAL_CH_V_SENS:
		adc_data.v_sens_ext_offset = raw_offset;
		config_store.calibration.v_sens_ext_offset = raw_offset;
		break;
	case CAL_CH_V_OUT:
		adc_data.v_out_offset = (uint16_t) raw_offset;
		config_store.calibration.v_out_offset = (uint16_t) raw_offset;
		break;
	case CAL_CH_V_HV:
		adc_data.v_hv_offset = (uint16_t) raw_offset;
		config_store.calibration.v_hv_offset = (uint16_t) raw_offset;
		break;
	case CAL_CH_I_OUT:
		adc_data.i_out_offset = (uint16_t) raw_offset;
		config_store.calibration.i_out_offset_ma = (uint16_t) raw_offset;
		if (raw_ext_offset) {
			adc_data.i_out_ext_offset = *raw_ext_offset;
			config_store.calibration.i_out_ext_offset = *raw_ext_offset;
		}
		break;
	case CAL_CH_I_ISO:
		adc_data.i_iso_offset = (uint16_t) raw_offset;
		config_store.calibration.i_iso_offset_ua = (uint16_t) raw_offset;
		if (raw_ext_offset) {
			adc_data.i_iso_ext_offset = *raw_ext_offset;
			config_store.calibration.i_iso_ext_offset = *raw_ext_offset;
		}
		break;
	case CAL_CH_V_IN:
		adc_data.v_in_offset = (uint16_t) raw_offset;
		config_store.calibration.v_in_offset_mv = (uint16_t) raw_offset;
		break;
	default:
		return;
	}
	config_store_store();
}

calibration_status_t calibration_set_gain_raw(calibration_channel_t ch, float gain, const float *ext_gain) {
	if (!calibration_gain_valid(gain))
		return CALIBRATION_STATUS_ERR;
	if (ext_gain && !calibration_gain_valid(*ext_gain))
		return CALIBRATION_STATUS_ERR;

	switch (ch) {
	case CAL_CH_V_TERM:
		adc_data.v_term_gain = gain;
		config_store.calibration.v_term_gain = gain;
		if (ext_gain) {
			adc_data.v_term_ext_gain = *ext_gain;
			config_store.calibration.v_term_ext_gain = *ext_gain;
		}
		break;
	case CAL_CH_V_SENS:
		adc_data.v_sens_ext_gain = gain;
		config_store.calibration.v_sens_ext_gain = gain;
		break;
	case CAL_CH_V_OUT:
		adc_data.v_out_gain = gain;
		config_store.calibration.v_out_gain = gain;
		break;
	case CAL_CH_V_HV:
		adc_data.v_hv_gain = gain;
		config_store.calibration.v_hv_gain = gain;
		break;
	case CAL_CH_I_OUT:
		adc_data.i_out_gain = gain;
		config_store.calibration.i_out_gain = gain;
		if (ext_gain) {
			adc_data.i_out_ext_gain = *ext_gain;
			config_store.calibration.i_out_ext_gain = *ext_gain;
		}
		break;
	case CAL_CH_I_ISO:
		adc_data.i_iso_gain = gain;
		config_store.calibration.i_iso_gain = gain;
		if (ext_gain) {
			adc_data.i_iso_ext_gain = *ext_gain;
			config_store.calibration.i_iso_ext_gain = *ext_gain;
		}
		break;
	case CAL_CH_V_IN:
		adc_data.v_in_gain = gain;
		config_store.calibration.v_in_gain = gain;
		break;
	default:
		return CALIBRATION_STATUS_ERR;
	}
	config_store_store();
	return CALIBRATION_STATUS_OK;
}

calibration_status_t calibration_set_gain(calibration_channel_t ch, float reference_value) {
	int32_t raw, raw_ext;
	float gain = 0.0f;
	float ext_gain = 0.0f;
	uint8_t has_ext = calibration_ext_index(ch) >= 0;

	calibration_sample_pair(ch, &raw, &raw_ext);

	int32_t offset = calibration_get_offset(ch);
	if (raw != offset)
		gain = reference_value / (float) (raw - offset);

	if (has_ext) {
		int32_t ext_offset = calibration_get_ext_offset(ch);
		if (raw_ext != ext_offset)
			ext_gain = reference_value / (float) (raw_ext - ext_offset);
	}

	// Reject the whole commit -- neither adc_data nor config_store is
	// touched, and config_store_store() is never called -- if the primary
	// gain, or (for channels with an ext counterpart) the ext gain, isn't
	// usable. Both are sampled from the same reference application, so a
	// bad ext result is just as much a sign that no real second point was
	// applied as a bad primary result is.
	if (!calibration_gain_valid(gain) || (has_ext && !calibration_gain_valid(ext_gain)))
		return CALIBRATION_STATUS_ERR;

	switch (ch) {
	case CAL_CH_V_TERM:
		adc_data.v_term_gain = gain;
		config_store.calibration.v_term_gain = gain;
		adc_data.v_term_ext_gain = ext_gain;
		config_store.calibration.v_term_ext_gain = ext_gain;
		break;
	case CAL_CH_V_SENS:
		adc_data.v_sens_ext_gain = gain;
		config_store.calibration.v_sens_ext_gain = gain;
		break;
	case CAL_CH_V_OUT:
		adc_data.v_out_gain = gain;
		config_store.calibration.v_out_gain = gain;
		break;
	case CAL_CH_V_HV:
		adc_data.v_hv_gain = gain;
		config_store.calibration.v_hv_gain = gain;
		break;
	case CAL_CH_I_OUT:
		adc_data.i_out_gain = gain;
		config_store.calibration.i_out_gain = gain;
		adc_data.i_out_ext_gain = ext_gain;
		config_store.calibration.i_out_ext_gain = ext_gain;
		break;
	case CAL_CH_I_ISO:
		adc_data.i_iso_gain = gain;
		config_store.calibration.i_iso_gain = gain;
		adc_data.i_iso_ext_gain = ext_gain;
		config_store.calibration.i_iso_ext_gain = ext_gain;
		break;
	case CAL_CH_V_IN:
		adc_data.v_in_gain = gain;
		config_store.calibration.v_in_gain = gain;
		break;
	default:
		return CALIBRATION_STATUS_ERR;
	}
	config_store_store();
	return CALIBRATION_STATUS_OK;
}
